nanbuwks/Esp32DualDialSsr/arduino-esp32/ESP32_DUALDIAL_checkflash/myFont40.cpp

// このファイルは「日本語フォントサブセットジェネレーター for LovyanGFX」によって生成されました。
// https://github.com/yamamaya/lgfxFontSubsetGenerator
// フォントデータは、文字情報技術促進協議会によるIPAフォントから派生した、LovyanGFX内の日本語フォントに基づ>いています。
// LovyanGFX
// https://github.com/lovyan03/LovyanGFX
// IPAフォントのライセンスについては以下を参照してください。
// https://moji.or.jp/ipafont/license/
// このソースをスケッチに追加した後、フォントを利用するソースには、以下の定義を追加してください。
// extern const lgfx::U8g2font myFont40;
// フォントを使用するときは、以下のようにsetFont関数で指定してください。
// lcd.setFont(&myFont40);

#include <LovyanGFX.hpp>

const uint8_t myFont40_data[753] = {
    0x49, 0x00, 0x04, 0x03, 0x06, 0x06, 0x07, 0x07, 0x07, 0x28, 0x28, 0x00, 0xFB, 0x1E, 0xFC, 0x21,
    0xFD, 0x00, 0x00, 0x00, 0x00, 0x01, 0xF0, 0x20, 0x07, 0x00, 0x00, 0x04, 0x52, 0x01, 0x30, 0x4D,
    0x90, 0x27, 0x0C, 0x52, 0xCB, 0xF2, 0x20, 0xEE, 0x60, 0x8A, 0x88, 0x68, 0x6C, 0x86, 0x8C, 0x64,
    0x8E, 0x64, 0xAC, 0x64, 0xAC, 0x64, 0x2C, 0x62, 0x82, 0x4A, 0xE2, 0x20, 0x2A, 0xE4, 0x20, 0x48,
    0xE4, 0x20, 0x48, 0xE4, 0x20, 0x46, 0xE6, 0x20, 0x46, 0xE6, 0x20, 0x44, 0xE8, 0x20, 0x44, 0xE8,
    0x20, 0x24, 0xEA, 0x20, 0x42, 0x8A, 0x62, 0x22, 0x6C, 0xA4, 0x6C, 0xA4, 0x6C, 0x84, 0x6E, 0x84,
    0x8C, 0x66, 0x6C, 0x88, 0xD5, 0xC1, 0xDC, 0x41, 0xA4, 0x15, 0x00, 0x31, 0x11, 0x07, 0x57, 0x14,
    0x52, 0x69, 0x86, 0xE2, 0xE0, 0x40, 0x82, 0x66, 0x68, 0xFF, 0xFF, 0x1F, 0x32, 0x26, 0x50, 0x27,
    0x14, 0x52, 0xCB, 0xF2, 0x40, 0xEA, 0xA0, 0x88, 0xA8, 0x84, 0x8C, 0x64, 0x70, 0x64, 0xF0, 0xF2,
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
};
extern const lgfx::U8g2font myFont40 = { myFont40_data };

// 収録されている文字の一覧
// U+0020 " ", U+0030 "0", U+0031 "1", U+0032 "2", U+0033 "3", U+0034 "4", U+0035 "5", U+0036 "6"
// U+0037 "7", U+0038 "8", U+0039 "9", U+610F "意", U+6CE8 "注"
